zzertexx/GPS-Tracker/Firmware/src/gps.c

#include "gps.h"
#include "uart_switch.h"
#include <zephyr/kernel.h>
#include <stdlib.h>
#include <string.h>
#include <zephyr/sys/printk.h>

#define PMTK_STANDBY  "$PMTK161,0*28\r\n"
#define PMTK_WAKE     "$PMTK010,001*2E\r\n"

#define GPS_LINE_MAX  96u

static gps_fix_t  m_fix;
static char       m_line[GPS_LINE_MAX];
static uint8_t    m_line_len;

static double nmea_coord_to_decimal(const char *field, char hem)
{
    if (field[0] == '\0') {
        return 0.0;
    }
    int degree_digits = (hem == 'N' || hem == 'S') ? 2 : 3;

    char deg_str[4] = {0};
    memcpy(deg_str, field, degree_digits);

    double degrees = atof(deg_str);
    double minutes  = atof(field + degree_digits);
    double decimal  = degrees + (minutes / 60.0);

    if (hem == 'S' || hem == 'W') {
        decimal = -decimal;
    }
    return decimal;
}

static int split_fields(char *line, char *fields[], int max_fields)
{
    int count = 0;
    char *tok = line;

    while (count < max_fields) {
        fields[count++] = tok;
        char *comma = strchr(tok, ',');
        if (!comma) {
            break;
        }
        *comma = '\0';
        tok    = comma + 1;
    }
    return count;
}

static bool parse_gga(char *sentence)
{
    char *fields[15];
    int n = split_fields(sentence, fields, 15);

    if (n < 8) {
        return false;
    }

    int quality = atoi(fields[6]);
    if (quality == 0) {
        m_fix.valid = false;
        return false;
    }

    m_fix.latitude   = nmea_coord_to_decimal(fields[2], fields[3][0]);
    m_fix.longitude  = nmea_coord_to_decimal(fields[4], fields[5][0]);
    m_fix.satellites = (uint8_t)atoi(fields[7]);
    m_fix.valid      = true;
    return true;
}

static bool process_line(char *line)
{
    if (line[0] != '$') {
        return false;
    }

    char *star = strchr(line, '*');
    if (star) {
        *star = '\0';
    }

    if (strncmp(line + 1, "GPGGA", 5) == 0 ||
        strncmp(line + 1, "GNGGA", 5) == 0) {
        return parse_gga(line);
    }
    return false;
}

bool gps_feed_byte(uint8_t byte)
{
    if (byte == '\r') {
        return false;
    }
    if (byte == '\n') {
        bool got_fix = false;
        if (m_line_len > 0) {
            m_line[m_line_len] = '\0';
            got_fix = process_line(m_line);
        }
        m_line_len = 0;
        return got_fix;
    }
    if (m_line_len < GPS_LINE_MAX - 1u) {
        m_line[m_line_len++] = byte;
    }
    return false;
}

gps_fix_t gps_get_fix(void)
{
    return m_fix;
}

void gps_init(void)
{
    memset(&m_fix, 0, sizeof(m_fix));
    m_line_len = 0;
}

void gps_enter_standby(void)
{
    uart_switch_to_gps();
    uart_write_str(PMTK_STANDBY);
    k_sleep(K_MSEC(200));
}

bool gps_acquire_fix(gps_fix_t *fix, int timeout_ms)
{
    uart_switch_to_gps();
    uart_flush_rx();

    uart_write_str(PMTK_WAKE);

    int64_t deadline = k_uptime_get() + timeout_ms;
    uint8_t byte;

    while (k_uptime_get() < deadline) {
        if (!uart_read_byte(&byte, K_MSEC(200))) {
            continue;
        }
        if (gps_feed_byte(byte) && m_fix.valid) {
            *fix = m_fix;
            printk("GPS fix: lat=%d.%06d lon=%d.%06d sats=%u\n",
                   (int)m_fix.latitude,
                   (int)((m_fix.latitude < 0 ? -m_fix.latitude : m_fix.latitude) * 1e6) % 1000000,
                   (int)m_fix.longitude,
                   (int)((m_fix.longitude < 0 ? -m_fix.longitude : m_fix.longitude) * 1e6) % 1000000,
                   m_fix.satellites);
            return true;
        }
    }

    printk("GPS: fix timeout\n");
    return false;
}
